2900xt/keiko-hackMIT/training/dataset/catalog/survey_registries_endpoints.md

# Machine-readable marine bioacoustics data sources — verified catalogue (checked 2026-09-19)

Legend: **V** = I fetched the page / listed the bucket / hit the API myself. **U** = unverified (from search snippets or secondary sources only). Sizes marked ">=" come from bucket scans that I capped at 12,000 objects.

## Headline findings
1. **Watkins (WHOI) is offline right now.** Both `cis.whoi.edu` and the `whoicf2.whoi.edu` mirror 302-redirect to `https://maintenance.whoi.edu` (curl + WebFetch, 2026-09-19). Everything below about its URL patterns comes from the Wayback Machine capture of 2024-08-10 (`web.archive.org/web/20240810115606id_/...`). The BEANS GCS zip (882 MB) and the Hugging Face parquet mirrors are the working fallbacks.
2. **The NCEI Google Cloud bucket `noaa-passive-bioacoustic` is the single richest anonymous endpoint**: it holds DCLDE 2011/2013/2015/2018/2022/2027, NEFSC, PIFSC, SanctSound, NRS, ADEON, JASCO, etc., all listable with no credentials via the JSON API.
3. **The Kaggle Watkins mirror (`shreyj1729/best-of-watkins-marine-mammal-sound-database`) returns 404** on both URL forms; treat it as gone. The Cornell/Right-Whale-Redux competition pages are JS-rendered (only `<meta>` text is fetchable), so their clip counts below are U.
4. **mobysound.org is dead** (parked Bluehost page). The DCLDE 2001–2013 archives it hosted are partially re-homed in the NCEI bucket (`dclde/2011/`, `dclde/2013/`).

## Master table

| Name | URL | Access | Format | Size | Species / scope | Labels | License | Download mechanics / URL patterns |
|---|---|---|---|---|---|---|---|---|
| **Watkins Marine Mammal Sound Database ("Best of" cuts)** V (via Wayback) | https://cis.whoi.edu/science/B/whalesounds/index.cfm (mirror: https://whoicf2.whoi.edu/science/B/whalesounds/) | Direct HTTP (currently down, maintenance redirect) | WAV, one file per cut; page table columns: `Sound cut file | Location | Observation Date | Download link | Metadata` | 1,694 cuts (about.cfm), 32 species; Internet-Archive zip of the 12 whale species is 646 MB | 32 species (list below) | Yes: species = page, plus per-cut location/date/metadata page | "free to download for personal or academic (not commercial) use. Reposting this work on third party websites is not permitted." Credit: "Watkins Marine Mammal Sound Database, Woods Hole Oceanographic Institution and the New Bedford Whaling Museum" | Species index page: `index.cfm` (dropdown `<option value="https://whoicf2.whoi.edu/science/B/whalesounds/bestOf.cfm?code=XXXX">`). Species page: `bestOf.cfm?code=AA3A` (54 WAV links on the N. right whale page). WAV href: `/science/B/whalesounds/WhaleSounds/<8-char id>.wav`, e.g. `https://cis.whoi.edu/science/B/whalesounds/WhaleSounds/5601601O.wav`, `.../56017007.wav`, `.../5900300A.wav` (id = 2-digit year + 3-digit tape + 3-char cut). Scraper that implements exactly this: https://github.com/AbdullahAbdelaziz122/watkins-mammal-scraper |
| **Watkins "All cuts"** V (Wayback) | `https://cis.whoi.edu/science/B/whalesounds/fullCuts.cfm` | Direct HTTP (down) | WAV | ~15,000 clips ("approximately 15,000 annotated digital sound clips"); HF mirror has 15,200 rows | 55 common names / 66 scientific-name codes (list below) | Yes | as above | Query pattern: `fullCuts.cfm?SP=<code>&YR=-1` (e.g. `fullCuts.cfm?SP=AC1E&YR=-1` = blue whale); master tapes at `masterFiles.cfm` |
| Watkins mirror: **BEANS zip** V | https://storage.googleapis.com/ml-bioacoustics-datasets/watkins.zip | Direct HTTP, no auth | WAV + `annotations.csv` (cols `path`, `species`) | 882,137,083 bytes | 32 species; BEANS drops Weddell_Seal (2 clips) -> 31 classes | Yes (CSV) | inherits Watkins terms | `wget https://storage.googleapis.com/ml-bioacoustics-datasets/watkins.zip && unzip watkins.zip -d watkins/` (this is exactly `scripts/watkins.py` in earthspecies/beans) |
| Watkins mirror: **HF DBD-research-group/beans_watkins** V | https://huggingface.co/datasets/DBD-research-group/beans_watkins | HF hub | parquet (train/train_low/valid/test) | 1K–10K rows | 31 classes (BEANS split) | Yes | not declared on card | `datasets.load_dataset("DBD-research-group/beans_watkins")` |
| Watkins mirror: **HF ivangtorre/watkins-marine-mammal-full-cuts** V | https://huggingface.co/datasets/ivangtorre/watkins-marine-mammal-full-cuts | HF hub | parquet, 9 shards, audio + nested metadata (record no., date, location+coords, signal/sound/animal dicts, sample rate 10–30 kHz) | 15,200 recordings | card says 54 species | Yes (species + Watkins metadata) | not declared | `load_dataset("ivangtorre/watkins-marine-mammal-full-cuts")` |
| Watkins mirror: **HF ardavey/marine_ocean_mammal_sound** V | https://huggingface.co/datasets/ardavey/marine_ocean_mammal_sound | HF hub | parquet | 1K–10K | 32 species (best-of) | Yes | card copies Watkins non-commercial text | `load_dataset("ardavey/marine_ocean_mammal_sound")` |
| Watkins mirror: **HF josegg5/watkins_marine_mammals_full** V | https://huggingface.co/datasets/josegg5/watkins_marine_mammals_full | HF hub | raw WAV in `Species/Year/<id>.wav` folders (127 files) | small (<1K) | partial | folder = species | tagged MIT (dubious relabel) | `huggingface-cli download josegg5/watkins_marine_mammals_full --repo-type dataset` |
| Watkins mirror: **Internet Archive watkins_best_of_whales_202008** V | https://archive.org/details/watkins_best_of_whales_202008 | Direct HTTP / torrent | per-species ZIPs | 646 MB total (`sperm_whale.zip` 446 MB, `short_finned_pilot_whale.zip` 121 MB, ... `minke_whale.zip` 48 KB) | 12 whale species only | folder = species | Watkins non-commercial | `https://archive.org/download/watkins_best_of_whales_202008/watkins_best_of_whales.zip`; metadata JSON at `https://archive.org/metadata/watkins_best_of_whales_202008` |
| Watkins **Kaggle mirror** (shreyj1729) | https://www.kaggle.com/datasets/shreyj1729/best-of-watkins-marine-mammal-sound-database | — | — | — | (55 folders per old descriptions) | — | — | **404 on 2026-09-19** (both `/datasets/` and `/shreyj1729/...` forms). Do not rely on it. |
| **DCLDE 2027 (ex-2026) killer whale dataset** V | GCS `gs://noaa-passive-bioacoustic/dclde/2027/dclde_2027_killer_whales/`; DOI https://doi.org/10.25921/15ey-mh50 (NCEI landing: `data.noaa.gov/metaview/page?xml=NOAA/NESDIS/NGDC/MGG/passive_acoustic//iso/xml/DCLDE_2027_Killer_Whales.xml&view=getDataView`); paper https://pmc.ncbi.nlm.nih.gov/articles/PMC12229703/ ; code https://zenodo.org/records/15743034 (10.5281/zenodo.15743034, MIT, 4.9 MB) | GCS anonymous | FLAC/WAV audio (16–256 kHz, provider-dependent) + `Annotations.csv` (50.5 MB) + per-provider `annotations/*.csv`, `metadata/*.pdf|txt` | paper: 1.6 TB, 225,000+ bounding-box annotations, 23 sites, May 2013–Apr 2023; my scan: >=253 GB in first 12,000 objects | *Orcinus orca* ecotypes SRKW, NRKW, TKW (Bigg's), OKW, SAR + humpback + abiotic + undetermined bio | Yes, CSV cols: `SoundFile, FilePath, FileBeginSec, FileEndSec, LowFreqHz, HighFreqHz, UTC, ClassSpecies, AnnotationLevel, KW, KW_certain, Ecotype, Data Provider, Dataset`; ClassSpecies in {KW, HW, AB, UndBio} | Bucket contains `CC-BY-4.0.txt`; the Sci Data paper states CC BY-NC-ND 4.0 — conflicting, check before commercial use | `gsutil -m cp -r gs://noaa-passive-bioacoustic/dclde/2027/dclde_2027_killer_whales/Annotations.csv .`; list: `curl "https://storage.googleapis.com/storage/v1/b/noaa-passive-bioacoustic/o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"`. Provider subfolders seen: `dfo_crp/`, `dfo_wdlp/` (files like `SOGN-AMAR-610_annotations.csv`) |
| **DCLDE 2027 NARW Cape Cod Bay** V | `gs://noaa-passive-bioacoustic/dclde/2027/dclde2027_narw_detections_in_cape_cod_bay/` + `.../dclde2027_acoustic_monitoring_in_cape_cod_bay/audio/` | GCS anonymous | Raven selection tables `data/YYYYMMDD.selections.txt` (122 objects, 0.3 GB) + 2 kHz FLAC 15-min files `85941ORSUCCB01_002K_M05_multi_20190215_155344Z.flac` (~3.3 MB each) | annotations 0.3 GB; audio Feb–Mar 2019 | North Atlantic right whale upcalls | Yes (Raven) | NOAA (public) | `gsutil -m cp -r gs://noaa-passive-bioacoustic/dclde/2027/dclde2027_narw_detections_in_cape_cod_bay/ .` |
| **DCLDE 2027 DAS fin-whale localization** V | `gs://noaa-passive-bioacoustic/dclde/2027/dclde_2027_das-finwhale-localization/` | GCS anonymous | DAS data + `annotations/batch1|batch2/annotated_calls_{north,south}_<timestamp>.csv` | 242 objects, 103.1 GB | fin whale 20 Hz calls (OOI DAS cable, Nov 2021) | Yes (CSV) | NOAA | as above |
| **DCLDE 2024 (Rotterdam)** V page | http://www.dclde2024.com/data-sets/ | **Request**: credentials in the dataset report (v5.0-1) downloaded from the page; weekly transfer via dclde2024@gmail.com; hosted on DRDC site | sonobuoy audio + CSV submission format | not stated ("batch download in progress") | NARW, Gulf of St Lawrence 2018, 2 x 3.5 h fields of 32 sonobuoys + visual/glider data | Yes | none stated | Not in the NCEI bucket (no `dclde/2024/` prefix). |
| **DCLDE 2022 (Oahu, HICEAS 2017)** V bucket | `gs://noaa-passive-bioacoustic/dclde/2022/dclde_2022_1705/` and `.../dclde_2022_1706/`; NCEI `gov.noaa.ncei.pad:DCLDE_2022_Raw_Data`; https://www.soest.hawaii.edu/ore/dclde/dataset/ (ECONNREFUSED on test) | GCS anonymous | WAV/FLAC towed-array multichannel | >=2.2 TB scanned (truncated); SOEST says ~8 TB uncompressed / 4 TB FLAC | beaked whales, minke boings, delphinids etc., Hawaiian EEZ Jul–Nov 2017 | Yes per SOEST (encounter tables); annotation files not located in my scan | NOAA | `gsutil ls gs://noaa-passive-bioacoustic/dclde/2022/` |
| **DCLDE 2018 (Paris)** V | https://sabiod.lis-lab.fr/DCLDE/challenge.html (self-signed cert; use `curl -k`) + `gs://noaa-passive-bioacoustic/dclde/2018/{audio,products}/` | Direct HTTP + Google Drive + GCS; HF audio originally by mailed 4 TB disk | WAV `WAT_HZ_01_151014_055500.x.wav` (200 kHz HF) / `HAT_A_02_121021_000000.d100.x.wav` (2 kHz LF); CSV annotations | GCS products 106 objects; audio prefix present (not sized) | HF: Gervais', Cuvier's, Sowerby's beaked whales, Atlantic white-sided, Risso's, short-finned pilot, *Stenella* sp., Delphinid A/B, unid. delphinid. LF: blue whale tonal, NARW upcall | Yes | none stated | LF annotations direct: `https://sabiod.lis-lab.fr/DCLDE/data/DCL_LF_Data_traindev/annotations/LF_Annotations_Dev.zip`; LF WAV Google Drive ids `1OPt9UXgWL6KpZpRekNdg_CeK4MONW5o3`, `1aHWlxViFktIoKqz-ObQB3NNuqp_wt5fb`, `1w9GumQTwkCDNKd_Vj24wT-Cx0i42tsBj`; scoring tools `files/dclde2018-scoringtools.zip`; NCEI CSVs e.g. `dclde/2018/products/detections/dclde_2018_hat-a_annotations_hf_dev/data/HAT_A_HF_dev.csv` (sites GofMX-DT, HAT-A, ...) |
| **DCLDE 2015 (San Diego)** V | https://www.cetus.ucsd.edu/dclde/dataset.html + `gs://noaa-passive-bioacoustic/dclde/2015/{audio,products}/` | Google Drive (LF) / mailed 4 TB disk via dcldeworkshop@gmail.com (HF) / GCS | HARP WAV; CSV call-level annotations | LF ~29 GB; GCS products 211 objects 4.5 GB | LF: blue whale D calls, fin 40 Hz; HF: Cuvier's & Baird's beaked, Risso's, Pacific white-sided, sperm, porpoise (to 160 kHz) | Yes | none stated | Drive: data `0B9myW-wOt9CLcVBvN01jNWFSQ0U`, annotations `0B9myW-wOt9CLQ2lyXzdkeVRoYWc`; GCS CSVs e.g. `dclde/2015/products/detections/dclde_2015_cinms-b_annotations_lf_eval/data/CINMS-B.csv` (sites CINMS-B, CINMS-C, DCPP-A, ...) |
| **DCLDE 2013 (St Andrews)** V | https://research-portal.st-andrews.ac.uk/en/datasets/dclde-2013-workshop-dataset/ (DOI 10.17630/62c3eebc-5574-4ec0-bfef-367ad839fe1a) and `gs://noaa-passive-bioacoustic/dclde/2013/nefsc_sbnms_200903_nopp6_ch10/` (NCEI DOI 10.25921/zaea-1s39) | Direct HTTP / GCS | WAV 15-min mono 2 kHz 16-bit (`NOPP6_EST_20090328_000000_CH10.wav`, 3,600,044 B each) + CSV logs | ~3.3 GB (St Andrews) | NARW upcalls, Cape Cod Bay / Great South Channel 2000–2009; SBNMS Mar 2009 all-baleen log | Yes: `detections/..._upcall-detection-log.csv`, `..._allbaleen_detection_log_updated-2025-07-02.csv` | CC BY (St Andrews) | `gsutil -m cp -r gs://noaa-passive-bioacoustic/dclde/2013/ .` |
| DCLDE 2011 | `gs://noaa-passive-bioacoustic/dclde/2011/` | GCS | — | not explored | Mt Hood workshop data | — | NOAA | prefix exists (listed) |
| **MobySound / DCL 2003–2009** | https://www.mobysound.org/workshops.html | **dead** | — | — | — | — | — | Domain is a parked Bluehost page (curl 2026-09-19). |
| **Orcasound live/archival audio** V | https://github.com/orcasound/orcadata (access.md) | S3 anonymous (`--no-sign-request`) | HLS `.ts` segments + `live.m3u8`; FLAC lossless (48/96/192 kHz) in archive bucket | continuous since 2018 (not sized) | SRKW habitat, 8 nodes | No (raw) | code AGPL-3.0; data CC BY-NC-SA per UKAN listing (U) | Buckets: `audio-orcasound-net` (live: `rpi_{andrews_bay,bush_point,mast_center,north_sjc,orcasound_lab,point_robinson,port_townsend,sunset_bay}/hls/<unix_ts>/`), `audio-deriv-orcasound-net`, legacy `streaming-orcasound-net`, `dev-streaming-orcasound-net`, `archive-orcasound-net` (FLAC; only `rpi_port_townsend/` present), `acoustic-sandbox`, `visual-sandbox`, `orcagsoc`. `aws --no-sign-request s3 ls s3://audio-orcasound-net/rpi_orcasound_lab/hls/` ; browse at https://open.quiltdata.com/b/acoustic-sandbox |
| **Orcasound Pod.Cast labeled rounds** V | https://github.com/orcasound/orcadata/wiki/Pod.Cast-data-archive ; `s3://acoustic-sandbox/labeled-data/detection/` | S3 anonymous | 20 kHz WAV + TSV (`dataset, wav_filename, start_time_s, duration_s, location, date, pst_or_master_tape_identifier`; positives only) | `train/TrainDataLatest_PodCastAllRounds_123567910.tar.gz` 5,461,870,195 B (8 rounds); `TrainDataLatest_PodCastAllRounds_123567.tar.gz` 3.5 GB; `TrainDataLatest_PodCastAllRounds.tar.gz` 2.13 GB; `TestDataLatest_PodCastAllRounds_123.tar.gz` 1.08 GB; `WHOIS09222019_PodCastRound1.tar.gz` 1.73 GB; `OrcasoundLab07052019_PodCastRound2.tar.gz` 259 MB; `OrcasoundLab09272017_PodCastRound3.tar.gz` 418 MB; `test/OS_SVeirs_07_05_2019_08_24_00.tar.gz` 134 MB; `test/OrcasoundLab09272017_Test.tar.gz` 95 MB; TSVs `podcast2.tsv`, `podcast3.tsv`, `test.tsv` | SRKW calls (binary) | Yes (TSV) | Round 1 is Watkins KW data with "different license"; rest Orcasound | `aws --no-sign-request s3 cp s3://acoustic-sandbox/labeled-data/detection/train/TrainDataLatest_PodCastAllRounds_123567910.tar.gz .` or `git clone https://github.com/orcasound/orcaml && python orcaml/data_ml/tools/download_datasets.py <dir>` |
| Orcasound classification sandbox V | `s3://acoustic-sandbox/labeled-data/classification/killer-whales/{biggs-transients,global-general/WMMSD,northern-residents,offshores,southern-residents}/` | S3 anonymous | e.g. `southern-residents/20190705/orcasound-lab/OS_7_05_2019_08_54_00_.wav` (317 MB) + Audacity label txt (`..._labels-SV_200210_only_calls.txt`) | few GB | KW ecotypes | partial | Orcasound | as above |
| Orcasound SRKW call catalog V | https://www.orcasound.net/data/product/SRKW/call-catalog/srkw-orca-call-catalog.html ; repo `orcadata/Sounds/catalog` | Direct HTTP / git | FLAC/OGG/MP3 + spectrograms | small | 41 SRKW call types S01–S46 (Ford 1987/Osborne) | call-type = file | not stated | git clone orcadata |
| **Kaggle Cornell Whale Detection Challenge (2013)** V page (JS-rendered) | https://www.kaggle.com/c/whale-detection-challenge/data | Kaggle account + accept rules | AIFF 2-s clips at 2 kHz; `train.csv` labels (U: 30,000 train / 54,503 test clips) | ~1 GB (U) | NARW upcall vs noise | Yes (binary CSV) | competition rules | `kaggle competitions download -c whale-detection-challenge`. Alt mirror: https://www.timeseriesclassification.com/description.php?Dataset=RightWhaleCalls |
| **Kaggle ICML 2013 Right Whale Redux** V page (JS) | https://www.kaggle.com/c/the-icml-2013-whale-challenge-right-whale-redux | Kaggle account | AIFF (U) | (U) | NARW upcall | Yes | competition rules | `kaggle competitions download -c the-icml-2013-whale-challenge-right-whale-redux` |
| **NOAA NCEI Passive Acoustic Data archive (GCS)** V | https://www.ncei.noaa.gov/products/passive-acoustic-data ; map https://www.ncei.noaa.gov/maps/passive-acoustic-data/ ; bucket https://console.cloud.google.com/storage/browser/noaa-passive-bioacoustic | GCS anonymous (also request via pad.info@noaa.gov) | WAV/FLAC/XWAV-in-FLAC; products netCDF + CSV | >100 TB total (NCEI) | 29 top-level prefixes: `MD_WEA_CPOD, adeon, aeon, afsc, big_query_metadata, boem, coastal_studies_institute, cornell, dclde, esons, fram, jasco, listen, mbarc_arctic, mbarc_cencal, mbarc_flip, mbarc_socal, mbari, navy, nefsc, nps, nrs, onms, pifsc, rutgers_njrmi, sanctsound, sefsc, soundcoop, swfsc` | per project; inventory CSVs in `big_query_metadata/` (`NCEI_NEFSC_PAD_metadata.csv` 33 MB, `NCEI_AFSC_PAD_metadata.csv`, `NCEI_SANCTSOUND_PAD_metadata.csv`, `NCEI_NRS_PAD_metadata.xlsx`, `NCEI_ADEON_PAD_metadata.xlsx`) | NOAA public domain / CC0 (SanctSound) | List: `curl "https://storage.googleapis.com/storage/v1/b/noaa-passive-bioacoustic/o?delimiter=/&prefix=<p>"`; fetch: `https://storage.googleapis.com/noaa-passive-bioacoustic/<object>`; `gsutil -m cp -r gs://noaa-passive-bioacoustic/<prefix> .` ; root `README.pdf` |
| **NEFSC annotated baleen datasets** V | https://www.fisheries.noaa.gov/resource/data/noaa-nefsc-north-atlantic-right-whale-acoustic-data-and-annotations ; `gs://noaa-passive-bioacoustic/nefsc/{audio,products}/` | GCS anonymous | multichannel audio + Raven-derived CSV logs (`Detected` / `Possibly_Detected`) | `nefsc/products/` = 4,316 objects, 32.4 GB (detections + sound_level_metrics netCDF) | NARW upcalls, humpback song, sei downsweeps, fin 20 Hz, minke pulse trains, blue A/B/AB | Yes: `nefsc/products/detections/nefsc_baleen/<deployment>_narw/data/<DEPLOY>_upcall-detection-log.csv` (e.g. `NEFSC_GA_201510_CH1_20160108_upcall-detection-log.csv`, `NEFSC_SBNMS_200712_NOPP1_CH10_20080127_...`, `NEFSC_NC_201712_HATTERAS_CH2_20180121_...`) | NOAA public | `gsutil -m cp -r gs://noaa-passive-bioacoustic/nefsc/products/detections/ .` ; deployment inventory (U, from search): `https://storage.googleapis.com/nmfs_odp_nefsc/PARR/READ/PSB/24687/24687_NEFSC_Acoustic_Deployments.xlsx`; PACM viewer https://apps-nefsc.fisheries.noaa.gov/pacm/ |
| **NOAA PIFSC HARP humpback set (Google model training data)** V | `gs://noaa-passive-bioacoustic/pifsc/` (README.md); DOI 10.25921/Z787-9Y54 | GCS anonymous | FLAC-compressed XWAV (75-s subchunks, 10 kHz; decompress with `flac -d --keep-foreign-metadata`) + `annotations.csv` | 9.2 TB (Google blog) | humpback song + confusers, 12 Pacific Islands sites, ~15 y | Yes: cols `audit_name, flac_compressed_xwav_object, subchunk_index, label_is_strong, ...` (Allen et al. 2021 Table 1) | NOAA public | `gsutil cp gs://noaa-passive-bioacoustic/pifsc/README.md .` |
| **SanctSound (NOAA/Navy)** V | https://catalog.data.gov/dataset/sanctsound-raw-passive-acoustic-data ; DOI 10.25921/saca-sp25 ; https://sanctsound.ioos.us/ | GCS anonymous | audio + per-detection CSV + netCDF | not stated; 30 sites x deployments 2018–21 | 7 sanctuaries + 1 monument; detection products per species (bluewhale, bocaccio, humpback, ...) | Yes | CC0 | `gs://noaa-passive-bioacoustic/sanctsound/audio/<site>/sanctsound_<site>_<dep>/` ; `.../products/detections/<site>/sanctsound_<site>_<dep>_<species>/data/SanctSound_<SITE>_<dep>_<species>.csv|.nc` (sites ci01–05, fk01–04, gr01–03, hi01,03–06, mb01–03, oc01–04, pm01,02,05,08, sb01–03) |
| **Google humpback whale model** V slug | https://www.kaggle.com/models/google/humpback-whale ; https://arxiv.org/abs/2512.03219 (Perch/whale) | Kaggle (kagglehub, free account) | TF2 SavedModel; 10 kHz input | — | humpback (trained on PIFSC HARP above) | model | Kaggle page JS-rendered; Apache-2.0 per perch repo (U) | `kagglehub.model_download("google/humpback-whale/tensorFlow2/humpback-whale")` (slug verified in perch-hoplite `kaggle_hub.py`) |
| **Google multispecies whale model** V | https://www.kaggle.com/models/google/multispecies-whale ; https://research.google/blog/whistles-songs-boings-and-biotwangs-recognizing-whale-vocalizations-with-ai/ | Kaggle | TF2 SavedModel | — | 8 species / 12 classes: humpback, killer whale (+echolocation, whistles), blue, fin, minke (boing), Bryde's (biotwang), N. Atlantic right, N. Pacific right (gunshot, upcall); training data from PIFSC, MBARI MARS, DFO Salish Sea, AFSC, NEFSC | model | as above | `kagglehub.model_download("google/multispecies-whale/tensorFlow2/default")`; hoplite key `multispecies_whale` |
| **Perch 2.0** V | https://www.kaggle.com/models/google/bird-vocalization-classifier (variant perch_v2) ; https://github.com/google-research/perch-hoplite ; paper https://arxiv.org/abs/2512.03219 | Kaggle | TF2 (GPU/CPU variants), ONNX port on HF | ~12M params EfficientNet-B3 | 14,597 species incl. mammals; whale transfer evaluated on Watkins/BEANS | model | Apache-2.0 (U) | `pip install git+https://github.com/google-research/perch-hoplite.git`; `model_configs.load_model_by_name('perch_v2')` -> slug `google/bird-vocalization-classifier/tensorFlow2/perch_v2` (or `perch_v2_cpu`); SurfPerch: `google/surfperch/TensorFlow2/1` |
| **MBARI MARS "pacific-sound" (AWS Open Data)** V | https://registry.opendata.aws/pacific-sound/ ; https://docs.mbari.org/pacific-sound/ | S3 anonymous, region us-west-2 | WAV: 16 kHz daily `s3://pacific-sound-16khz/YYYY/MM/MARS-YYYYMMDDT000000Z-16kHz.wav` (4,147,200,332 B/day); 2 kHz daily `s3://pacific-sound-2khz/YYYY/MM/MARS-YYYYMMDDT000000Z-2kHz.wav` (518 MB/day); raw 256 kHz 10-min `s3://pacific-sound-256khz-YYYY/MM/MARS_YYYYMMDD_HHMMSS.wav` (461 MB) | 2015–2026 continuous (~1.5 TB/yr at 16 kHz) | Monterey Bay: blue, fin, humpback, orca, dolphins, ships | Labeled subsets via docs notebooks (blue-whale call index, fin index, humpback song); models in `s3://pacific-sound-models/` (`bluewhale-a-resnet50-2022-02-05-...tar.gz` 254 MB, `bluewhale-d-efnetb0-...` 46 MB, etc.) | CC-BY 4.0 | `aws s3 ls --no-sign-request s3://pacific-sound-16khz/2023/01/` ; `aws s3 cp --no-sign-request s3://pacific-sound-2khz/2023/01/MARS-20230101T000000Z-2kHz.wav .` |
| **Ocean Networks Canada Oceans 3.0 API** V | https://oceannetworkscanada.github.io/Oceans3.0-API/API_Guide.html ; OpenAPI https://data.oceannetworks.ca/OpenAPI ; UI https://data.oceannetworks.ca/SearchHydrophoneData | **Registration** (free token: data.oceannetworks.ca/Registration -> Profile -> Web Services API -> Copy Token) | WAV/FLAC/MP3 archive files + spectrogram PNG; data products generated on demand | multi-year cabled hydrophones (BC coast, Arctic) | Salish Sea/Barkley Canyon etc. | No (raw); ONC-derived labels exist in HF `bnestor/marine_mammal_labels` (8,761 JSON, CC-BY-4.0, filenames like `ICLISTENAF2523_20160523T094302.000Z_...json`) | CC-BY-ND per UKAN (U); client Apache-2.0 | `pip install onc`; `from onc import ONC; onc=ONC(token); onc.getLocations({"deviceCategoryCode":"HYDROPHONE"}); onc.getArchivefileByLocation({...}); onc.downloadArchivefile(filename)`; endpoints `/api/archivefile`, `/api/dataProductDelivery` (request->run->download, or `orderDataProduct()`); last-hour WAVs withheld |
| **OOI hydrophones (Regional Cabled / Endurance)** V root | https://rawdata.oceanobservatories.org/files/ ; https://github.com/Ocean-Data-Lab/ooipy ; https://ooipy.readthedocs.io/ | Direct HTTP (raw data server; not in M2M API) | miniSEED 5-min files (broadband 64 kHz; low-freq 200 Hz) | 1.8 GB/hour broadband | NE Pacific (Oregon slope/axial): fin, blue, humpback, sperm, ships | No | OOI open data (CC0/public, U) | Directory tree `https://rawdata.oceanobservatories.org/files/<SITE>/<NODE>/<INSTR>/YYYY/MM/DD/` e.g. `RS01SLBS/LJ01A/09-HYDBBA102/` (site codes listed at root: AS03CPPM, CE01ISSM, CE02SHBP, CE04OSBP, RS01..., ...). `pip install ooipy; ooipy.get_acoustic_data(start,end,'LJ01A')` |
| **BEANS benchmark (earthspecies)** V | https://github.com/earthspecies/beans ; datasets.yml | mixed: GCS zips (marine ones) + Kaggle CLI (cbi, rcfx) | WAV + CSV splits | whole benchmark ~300 GB; marine parts: `watkins.zip` 882 MB, `hiceas_1-20_minke-detection.zip` 1,424,628,433 B | marine subsets: **watkins** (classification, 31 species, 44.1 kHz, <=3 s) and **hiceas** (detection, 1 label: minke boings, HICEAS towed array) | Yes | code MIT; data per source | `bash scripts/download_data.sh` (needs `~/.kaggle/kaggle.json`, sox); direct: `wget https://storage.googleapis.com/ml-bioacoustics-datasets/hiceas_1-20_minke-detection.zip` |
| **ANIMAL-SPOT data** V | https://github.com/ChristianBergler/ANIMAL-SPOT ; data DOI https://doi.org/10.17617/3.KQPPXF (Edmond/MPG Dataverse) | Direct HTTP (Dataverse) | `ANIMAL-SPOT_FILES.tar.gz` 547.4 MB (cropped audio, unseen prediction tape, splits, logs) | 547 MB | multi-species incl. orca (~5,000 samples/species) | Yes | CC BY 4.0 | Dataverse API: `https://edmond.mpg.de/api/datasets/:persistentId/?persistentId=doi:10.17617/3.KQPPXF` -> file id -> `/api/access/datafile/<id>` |
| **ORCA-SPOT** V | https://github.com/ChristianBergler/ORCA-SPOT | code only | — | trained on 11,509 KW signals + 34,848 noise (Orchive/OrcaLab NRKW) | NRKW | training data **not public** | GPL-3.0 (code) | Orchive (http://orchive.cs.uvic.ca/) availability uncertain |
| **Antarctic blue/fin whale annotated library (AAD)** V | https://data.aad.gov.au/metadata/records/fulldisplay/AcousticTrends_BlueFinLibrary ; DOI 10.26179/5e6056035c01b | Direct HTTP | 16-bit WAV at 250/500/1000/2000 Hz + Raven Pro 1.5 selection tables (TSV) | 1,880 h, 11 site-years 2005–2017, 105,161 annotations | Antarctic blue & fin whale calls (7 call types) | Yes | CC BY 4.0 | `https://data.aad.gov.au/eds/5091/download` |
| HF **monster-monash/WhaleSounds** V | https://huggingface.co/datasets/monster-monash/WhaleSounds | HF hub | `.npy`/CSV, 105,163 x 2,500 samples @250 Hz | 3.57 GB | 8 classes (7 Antarctic call types + unidentified), derived from AAD library | Yes | CC BY 4.0 | `load_dataset("monster-monash/WhaleSounds")` |
| HF **CIANLabxBROWNUniv/fin_whale_1** V | https://huggingface.co/datasets/CIANLabxBROWNUniv/fin_whale_1 | HF hub | 7,118 files (code + data) | — | fin whale detection (SSL vs supervised paper) | Yes | MIT | `huggingface-cli download ...` |
| **FRDR NARW upcalls Gulf of St Lawrence** V | https://www.frdr-dfdr.ca/repo/dataset/4a3113e6-1d58-6bb4-aaf2-a9adf75165be (DOI 10.20383/101.0241) | Globus (account) or zip (was unavailable) | audio + spectrograms + presence/absence annotations | not stated | NARW, 6 stations 2015–2019 + Gulf of Maine 2009 | Yes | CC BY 4.0 | Globus transfer |
| **DOCC10 (Dyni odontocete click classification)** V | https://challengedata.ens.fr/challenges/32 | **Registration** | raw click frames 8,192 samples @200 kHz | train ~6 GB; 11,312/class train, 2,096/class test | 10 classes: Risso's, short-finned pilot, Atl. white-sided, Sowerby's, Gervais', sperm whale, *Stenella*, delphinid A/B, Cuvier's (9 from DCLDE 2018 + DYNI Med sperm whales) | Yes (balanced) | not stated | login required |
| **Zenodo hits** (titles from search; only 15743034 fetched) | 10.5281/zenodo.20702261 glider PAM Cabrera (51.2 h @240 kHz, sperm/Risso's clicks + whistles, annotated) U; 10.5281/zenodo.22649833 E. Med dolphin whistle clips (713 common + 222 bottlenose) U; 10.5281/zenodo.10665971 Placentia Bay acoustic features U; 10.5281/zenodo.7886409 DAS + hydrophone array U; 10.5281/zenodo.5841998 porpoise hydrophone clusters (windfarm) U; 10.5281/zenodo.5823343 DAS4Whales U; 10.5281/zenodo.15743034 DCLDE code V (MIT) | Direct HTTP | mixed | — | — | — | — | Zenodo REST: `https://zenodo.org/api/records?q=<terms>&size=25` (note: complex boolean queries returned 400 / off-topic ranking; search manually) |
| **Dryad hits** V (API) | doi:10.5061/dryad.v9s4mw6xv harbour porpoise hydrophone array on gill net (6.76 GB, CC0); doi:10.5061/dryad.98sf7m0mn coastal acoustic buoy cetacean detections (9.85 GB, CC0); doi:10.5061/dryad.7h44j0zvq porpoise directional clusters at windfarms (U); doi:10.5061/dryad.3bk3j9kn8 Placentia Bay PAM features (U) | Direct HTTP | WAV/CSV | as listed | porpoise / cetacean | partial | CC0 | `https://datadryad.org/api/v2/search?q=cetacean+acoustic+recordings+hydrophone` |
| **Figshare** | Sci Data bottlenose dolphin trawling WAV dataset (s41597-023-02547-8, 192 kHz) U | Direct HTTP | WAV | — | *Tursiops* whistles/clicks/pulses | Yes | CC BY (U) | Figshare API search (`POST /v2/articles/search`) returned no relevant hits for my query; locate via the paper's Data Availability |
| **PANGAEA** V (API) | https://doi.pangaea.de/10.1594/PANGAEA.773610 PALAOA soundscape 2005–2011 (links to audio stream files, CC BY 3.0); 10.1594/PANGAEA.861766 PASATA field documentation (CC BY 3.0) | Direct HTTP | audio streams / docs | — | Antarctic (Weddell seals, leopard seals, orcas, minke) | No/partial | CC BY 3.0 | `https://www.pangaea.de/advanced/search.php?q=hydrophone+marine+mammal&count=15` (JSON) |
| **GBIF sound occurrences (marine)** V | https://api.gbif.org/v1/occurrence/search?taxonKey=733&mediaType=Sound | API, no auth | JSON with `media[].identifier` -> iNat `.m4a` | Cetacea (taxonKey 733): **120** sound occurrences (71 from iNaturalist dataset `50c9509d-22c7-4a22-a47d-8c48425ef4a7`, 30 from `f11db245-...`, 11 from `b7ec1bf8-...`); Pinnipedia (4941589): 0 | orca, harbour porpoise, humpback, etc. | species = label | per record (CC BY-NC mostly) | `&facet=datasetKey`, `&limit=300&offset=N` |
| **iNaturalist sounds** V | https://api.inaturalist.org/v1/observations?taxon_id=152871&sounds=true&quality_grade=research | API, no auth | `.m4a`/`.wav` at `https://static.inaturalist.org/sounds/<id>.m4a` | 128 obs (85 research-grade) for Cetacea | e.g. *Aethalodelphis obliquidens*, humpback | species | per obs (cc0, cc-by-nc, ...) | paginate `per_page=200&page=N`; `sounds[].file_url` |
| **Macaulay Library** | https://search.macaulaylibrary.org/catalog?mediaType=audio&taxonCode=<code> | Registration + cart request for originals; CSV metadata export | WAV/MP3 originals by request | ~2,159 Cetacea audio + 312 video (U) | cetaceans, sirenians, pinnipeds | species + metadata | ML terms (research request) | No bulk API; site 403s to bots |
| **DOSITS audio gallery** | https://dosits.org/galleries/audio-gallery/marine-mammals/ (403 to bots) | Direct HTTP (browser) | MP3 per species page | small | baleen, toothed, pinnipeds, sirenians | species page | per-file copyright (not bulk-licensed) | not machine-friendly |
| **Freesound MBARI_MARS pack** V | https://freesound.org/people/MBARI_MARS/packs/19487/ | Registration (login to download) / API token | WAV/FLAC | 12+ sounds | humpback, blue, gray, sperm, beaked, orca, Pacific white-sided | tags | per-sound CC | Freesound API `https://freesound.org/apiv2/search/text/?query=hydrophone&token=...`; other packs: klankbeeld 26803, 14861 |
| **IMOS acoustic observatories (AODN)** V | https://acoustic.aodn.org.au/acoustic/ ; S3 `s3://imos-data/IMOS/ANMN/Acoustic/` (ap-southeast-2) | S3 anonymous / portal | raw Curtin noise-logger `.DAT` (~2.4 MB each) + spectrogram PNG; Matlab reader in `code/`; `calibration/`, `metadata/` | 2008–2017 (ceased) | sites PAKAI (Kangaroo I.), PAKIM (Kimberley), PAPCA (Perth Canyon), PAPIL (Pilbara), PAPOR (Portland), PATUN (Tuncurry); pygmy blue, fin, humpback | No | IMOS CC-BY (U) | `aws s3 ls --no-sign-request s3://imos-data/IMOS/ANMN/Acoustic/PAPCA/2802/20080226/raw/` ; http listing `https://s3-ap-southeast-2.amazonaws.com/imos-data/?prefix=IMOS/ANMN/Acoustic/` |
| **JASCO** | https://www.jasco.com/public-reports | none open | — | — | contributed JASCO/VFPA orca data to DCLDE 2027; `jasco/audio/` prefix exists in NCEI bucket (V) | — | — | no public dataset endpoint |
| **AcousticNet** | — | — | — | — | **no such resource found** in 2 searches | — | — | — |
| **Marine Mammal Commission** | https://www.mmc.gov/wp-content/uploads/sound_bklet.pdf | — | PDF only | — | no data | — | — | not a data source |
| **UK Acoustics Network open-data list** V | https://acoustics.ac.uk/open-access-underwater-acoustics-data/ | index page | — | 95 entries (DCL/DCLDE, ALOHA, LoVe, Galway Bay, SOHN, OHA-SIS-BIO, DAS4Whales, ShipsEar, DeepShip...) | — | — | — | best secondary aggregator found |

## Species-name lists (verbatim from fetched pages)

### Watkins "Best of" cuts — code -> common name (index.cfm dropdown, Wayback 2024-08-10)
```
AA1A  Bowhead Whale                       BD15L Spinner Dolphin
AA3A  Northern Right Whale                BD17A Rough-Toothed Dolphin
AA3B  Southern Right Whale                BD19D Bottlenose Dolphin
AC1A  Minke Whale                         BD3B  Common Dolphin
AC1F  Fin, Finback Whale                  BD4A  Grampus, Risso's Dolphin
AC2A  Humpback Whale                      BD5A  Fraser's Dolphin
BA2A  Sperm Whale                         BD6A  White-sided Dolphin
BB1A  Beluga, White Whale                 BD6B  White-beaked Dolphin
BB2A  Narwhal                             BE3C  Long-Finned Pilot Whale
BD10A Melon Headed Whale                  BE3D  Short-Finned (Pacific) Pilot Whale
BD15A Pantropical Spotted Dolphin         BE7A  Killer Whale
BD15B Clymene Dolphin                     BE9A  False Killer Whale
BD15C Striped Dolphin                     CB1A  Walrus
BD15F Atlantic Spotted Dolphin            CC12G Harp Seal
                                          CC14A Ross Seal
                                          CC2A  Bearded Seal
                                          CC4A  Leopard Seal
                                          CC5A  Weddell Seal
```
Scientific names on the same page: AA1A *Balaena mysticetus*; AC1A *Balaenoptera acutorostrata*; AC1F *Balaenoptera physalus*; BB1A *Delphinapterus leucas*; BD3B *Delphinus delphis*; CC2A *Erignathus barbatus*; AA3B *Eubalaena australis*; AA3A *Eubalaena glacialis*; BE3C *Globicephala melas (Globicephala melaena, Globicephala edwardii)*; BE3D *Globicephala macrorhynchus (Globicephala scammoni)*; BD4A *Grampus griseus*; CC4A *Hydrurga leptonyx*; BD5A *Lagenodelphis hosei*; BD6A *Lagenorhynchus acutus*; BD6B *Lagenorhynchus albirostris*; CC5A *Leptonychotes weddellii*; AC2A *Megaptera novaeangliae*; BB2A *Monodon monoceros*; CB1A *Odobenus rosmarus*; CC14A *Ommatophoca rossi*; BE7A *Orcinus orca*; BD10A *Peponocephala electra*; CC12G *Pagophilus groenlandicus (Phoca groenlandica)*; BA2A *Physeter macrocephalus (Physeter catodon)*; BE9A *Pseudorca crassidens*; BD15A *Stenella attenuata*; BD15B *Stenella clymene*; BD15C *Stenella coeruleoalba*; BD15F *Stenella frontalis*; BD15L *Stenella longirostris*; BD17A *Steno bredanensis*; BD19D *Tursiops truncatus (Tursiops gilli)*.

### Watkins "All cuts" — code -> common name (fullCuts.cfm dropdown; query `fullCuts.cfm?SP=<code>&YR=-1`)
```
BD15F Atlantic Spotted Dolphin      CC2A  Bearded Seal              BB1A  Beluga, White Whale
AC1E  Blue Whale                    BD19D Bottlenose Dolphin        BG2A  Boutu, Amazon River Dolphin
AA1A  Bowhead Whale                 BD15B Clymene Dolphin           BD1A  Commerson's Dolphin
BD3B  Common Dolphin                BF4A  Dall's Porpoise           BD6H  Dusky Dolphin
BE9A  False Killer Whale            AC1F  Fin, Finback Whale        BF6A  Finless Porpoise
BD5A  Fraser's Dolphin              BD4A  Grampus, Risso's Dolphin  CC3A  Gray Seal
AB1A  Gray Whale                    BF2A  Harbor Porpoise           CC12V Harbour Seal
CC12G Harp Seal                     BD1C  Heaviside's Dolphin       CC1A  Hooded Seal
AC2A  Humpback Whale                BD12A Irawaddy Dolphin          CA1P  Juan Fernandez Fur Seal
BE7A  Killer Whale                  CC4A  Leopard Seal              BD3A  Long Beaked (Pacific) Common Dolphin
BE3C  Long-Finned Pilot Whale       BD10A Melon Headed Whale        AC1A  Minke Whale
BB2A  Narwhal                       CA1F  New Zealand Fur Seal      AA3A  Northern Right Whale
BD15A Pantropical Spotted Dolphin   CC12F Ribbon Seal               CC12H Ringed Seal
CC14A Ross Seal                     BD17A Rough-Toothed Dolphin     CD1A  Sea Otter
BE3D  Short-Finned (Pacific) Pilot Whale   AA3B Southern Right Whale   BA2A Sperm Whale
BD15L Spinner Dolphin               CC12L Spotted Seal              CA3B  Steller Sea Lion
BD15C Striped Dolphin               BD12B Tucuxi Dolphin            CB1A  Walrus
CC5A  Weddell Seal                  DB1B  West Indian Manatee       BD6B  White-beaked Dolphin
BD6A  White-sided Dolphin
```
Additional scientific-name codes present only in the All-cuts scientific dropdown (no common-name entry): CA2A *Callorhinus ursinus*; BE3A *Globicephala malaena (Globicephala edwardii)*; BD6C *Lagenorhynchus australis*; BD6G *Lagenorhynchus obliquidens*; CC6A *Lobodon carcinophaga (Lobodon carcinophagus)*; CC10A *Mirounga angustirostris*; CA6A *Otaria flavescens*; CA8A *Phocarctos hookeri*; BD19A *Tursiops catalania (Tursiops aduncus)*; CA9A *Zalophus californianus*; BC9A *Ziphius cavirostris*. (Other All-cuts scientific names map 1:1 to the common-name codes above, e.g. AC1E *Balaenoptera musculus*, AB1A *Eschrichtius robustus*, BG2A *Inia geoffrensis*, BF2A *Phocoena phocoena*, BF4A *Phocoenoides dalli*, BF6A *Neophocaena phocaenoides*, DB1B *Trichechus manatus*, CD1A *Enhydra lutris*, CC12V *Phoca vitulina*, CC12H *Pusa hispida*, CC12F *Histriophoca fasciata*, CC12L *Phoca largha*, CC3A *Halichoerus grypus*, CC1A *Cystophora cristata*, CA3B *Eumetopias jubatus*, CA1F *Arctocephalus forsteri*, CA1P *Arctocephalus philippii*, BD1A *Cephalorhynchus commersonii*, BD1C *Cephalorhynchus heavisidii*, BD3A *Delphinus capensis (Delphinus bairdii)*, BD6H *Lagenorhynchus obscurus*, BD12A *Sotalia borneensis*, BD12B *Sotalia fluviatilis*.) Code scheme: A = mysticetes, B = odontocetes, C = pinnipeds/otter, D = sirenians.

### DCLDE 2027 killer-whale labels (from the Sci Data paper)
ClassSpecies: `KW` (killer whale), `HW` (humpback), `AB` (abiotic), `UndBio` (undetermined biological). Ecotype: `SRKW`, `NRKW`, `TKW` (Bigg's/transient), `OKW` (offshore), `SAR` (Southern Alaska Resident).

### DCLDE 2018 high-frequency classes (verbatim)
*Mesoplodon europaeus* Gervais' beaked whale; *Ziphius cavirostris* Cuvier's beaked whale; *Mesoplodon bidens* Sowerby's beaked whale; *Lagenorhynchus acutus* Atlantic white-sided dolphin; *Grampus griseus* Risso's dolphin; *Globicephala macrorhynchus* short-finned pilot whale; *Stenella* sp.; Delphinid type A; Delphinid type B; Unidentified delphinid. Low-frequency: *Balaenoptera musculus* tonal calls; *Eubalaena glacialis* up-calls.

### Google multispecies-whale classes (research.google blog)
Humpback; killer whale (calls, echolocation, whistles); blue; fin; minke (boing); Bryde's (biotwang); North Atlantic right whale; North Pacific right whale (gunshot, upcall). 8 species / 12 classes.

### BEANS `watkins` (datasets.yml)
31 classes after dropping Weddell_Seal; names use underscores, e.g. `Bottlenose_Dolphin`, `Humpback_Whale`, `Killer_Whale`, `Walrus` (full list = the 32 Best-of species above, minus Weddell Seal).

## Notes / caveats
- Watkins Kaggle mirror: 404; Kaggle competition/model pages are client-rendered so file sizes/licenses on Kaggle are U (slugs are V via perch-hoplite source).
- DCLDE 2027 license conflict (bucket `CC-BY-4.0.txt` vs paper's CC BY-NC-ND 4.0) needs resolving with NCEI/authors before any commercial use.
- DCLDE 2022 SOEST site refused connections; DCLDE 2024 has no NCEI copy and needs the DRDC credentials from the report.
- Zenodo/Figshare full-text search APIs ranked off-topic records first; the Zenodo DOIs listed came from web search, not from API confirmation (except 15743034).
- Scratch files from the fetches are in `/tmp` (`watkins_index.html`, `wb_aa3a.html`, `wb_fullcuts.html`, `wb_about.html`, `zen.json`, `gbif.json`, `kg*.html`).
