2900xt/keiko-hackMIT/firmware/esp32-s3/sketch/hydro.cpp

//
// Samples the piezo follower on GPIO1 (ADC1_CH0) at a fixed rate from a
// high-priority FreeRTOS task paced by a hardware timer, and ships raw 12-bit
// ADC counts to the laptop in framed blocks over native USB CDC:
//
//   "KBLK" | seq | t0_us | dropped | n | n x int16 | crc16
//
//   seq      uint32  block counter
//   t0_us    uint32  esp_timer_get_time() at the first sample of the block
//   dropped  uint32  blocks overwritten because the sender could not keep up
//   n        uint16  samples in this block (BLOCK)
//   data     n x little-endian int16, raw ADC counts 0..4095
//   crc      uint16  CRC-16/CCITT-FALSE over everything before it
//
// Same shape as the UNO Q node's Bridge.notify("hydro/block", …), just on a
// wire with no message boundaries, hence the magic + CRC. USB CDC moves
// ~1 MB/s, so unlike the UNO Q's 115200-baud Bridge the sample rate is limited
// by the ADC conversion time (~25 us), not the link.
//
// Wi-Fi mode (no laptop): if sketch/wifi_config.h exists, the board joins that
// network and also sends each block as a ready-made KEIK datagram straight to
// the pipeline -- the packet python/main.py would otherwise build. The serial
// frames keep flowing whenever a host is attached, so both can be watched.

#include <Arduino.h>
#include <esp_timer.h>
#include <freertos/FreeRTOS.h>
#include <freertos/queue.h>
#include <freertos/semphr.h>
#include <freertos/task.h>

#if __has_include("wifi_config.h")
#include "wifi_config.h"                       // gitignored: copy wifi_config.h.example and fill it in
#include <WiFi.h>
#include <WiFiUdp.h>
#define KEIKO_WIFI 1
#else
#define KEIKO_WIFI 0
#endif

// ---- configuration ---------------------------------------------------------
static const uint32_t SAMPLE_PERIOD_US = 125;   // 8000 Hz. The 1 MHz timer makes this exact; the Python side still
                                                // measures the real rate from t0_us.
static const uint8_t  ADC_PIN          = 1;     // GPIO1 = ADC1_CH0. Stay on ADC1: ADC2 is unusable while Wi-Fi is on.
static const int      ADC_BITS         = 12;
static const size_t   BLOCK            = 256;   // samples per frame (512 bytes payload, ~31 frames/s at 8 kHz)
static const size_t   NBLOCKS          = 4;     // ring depth; sender may lag by NBLOCKS-1 blocks
static const BaseType_t SAMPLER_CORE   = 1;     // the app core (loop() runs there too; the sampler outranks it)

// ---- frame -----------------------------------------------------------------
struct __attribute__((packed)) FrameHeader {
  char     magic[4];
  uint32_t seq;
  uint32_t t0_us;
  uint32_t dropped;
  uint16_t n;
};

// KEIK datagram (see python/main.py PACKET FORMAT); built on the board in Wi-Fi mode
struct __attribute__((packed)) KeikHeader {
  char     magic[4];
  uint8_t  ver, node, fmt, bits;
  float    fs;
  uint32_t seq;
  uint64_t t_ns;
  uint16_t n;
};

static uint16_t crc16_ccitt(uint16_t crc, const uint8_t* p, size_t len) {
  while (len--) {
    crc ^= (uint16_t)(*p++) << 8;
    for (int i = 0; i < 8; i++) crc = (crc & 0x8000) ? (crc << 1) ^ 0x1021 : crc << 1;
  }
  return crc;
}

// ---- sampler <-> sender plumbing ------------------------------------------
static int16_t  ring[NBLOCKS][BLOCK];
static uint32_t ring_t0_us[NBLOCKS];
static uint32_t dropped_blocks = 0;

static QueueHandle_t     ready_q;     // depth NBLOCKS-1 keeps the block being filled private
static SemaphoreHandle_t tick_sem;    // binary: late ticks coalesce instead of piling up
static hw_timer_t*       tick_timer;

static void IRAM_ATTR on_tick() {
  BaseType_t woken = pdFALSE;
  xSemaphoreGiveFromISR(tick_sem, &woken);
  if (woken) portYIELD_FROM_ISR();
}

static void sampler(void*) {
  uint8_t b = 0;
  size_t  i = 0;
  ring_t0_us[b] = (uint32_t)esp_timer_get_time();
  for (;;) {
    xSemaphoreTake(tick_sem, portMAX_DELAY);
    int raw = analogRead(ADC_PIN);
    if (raw < 0) raw = 1 << (ADC_BITS - 1);   // adc error -> mid-scale, keeps timing intact
    ring[b][i++] = (int16_t)raw;
    if (i == BLOCK) {
      i = 0;
      if (xQueueSend(ready_q, &b, 0) == pdTRUE) {
        b = (b + 1) % NBLOCKS;
      } else {
        dropped_blocks++;                     // sender is behind: reuse this block, keep sampling
      }
      ring_t0_us[b] = (uint32_t)esp_timer_get_time();
    }
  }
}

// ---- Wi-Fi -----------------------------------------------------------------
#if KEIKO_WIFI
static WiFiUDP udp;
static float   fs_measured = 0;               // from consecutive block timestamps, same estimator as main.py
static uint32_t last_t0_us = 0;
static bool     have_last  = false;

static void wifi_begin() {
  WiFi.mode(WIFI_STA);
  WiFi.setSleep(false);                       // modem sleep adds 100s of ms of jitter to UDP sends
  WiFi.begin(KEIKO_WIFI_SSID, KEIKO_WIFI_PSK);
  WiFi.setAutoReconnect(true);                // dropouts are the node's problem, not the pipeline's
}

static void send_keik(uint32_t seq, uint32_t t0_us, const uint8_t* data) {
  if (have_last && seq) {                     // measure fs across consecutive blocks (blocks are never reordered here)
    uint32_t dt = t0_us - last_t0_us;
    if (dt) {
      float fs = BLOCK * 1e6f / dt;
      fs_measured = fs_measured == 0 ? fs : 0.9f * fs_measured + 0.1f * fs;
    }
  }
  last_t0_us = t0_us; have_last = true;
  if (WiFi.status() != WL_CONNECTED) return;

  KeikHeader k = {{'K', 'E', 'I', 'K'}, 1, KEIKO_NODE_ID, 0, (uint8_t)ADC_BITS, fs_measured, seq,
                  (uint64_t)esp_timer_get_time() * 1000ULL, (uint16_t)BLOCK};
  udp.beginPacket(KEIKO_UDP_HOST, KEIKO_UDP_PORT);
  udp.write(reinterpret_cast<const uint8_t*>(&k), sizeof k);
  udp.write(data, BLOCK * sizeof(int16_t));
  udp.endPacket();
}
#endif

// ---- Arduino ---------------------------------------------------------------
void setup() {
  Serial.begin(921600);                       // baud is ignored on native USB CDC; matters only if Serial is a UART
  Serial.setTxTimeoutMs(50);                  // no host reading -> writes give up instead of stalling the sender
#if KEIKO_WIFI
  wifi_begin();
#endif
  analogReadResolution(ADC_BITS);
  analogSetPinAttenuation(ADC_PIN, ADC_11db); // 0..~3.1 V full scale; the follower idles at ~1.7 V
  analogRead(ADC_PIN);                        // first call does the channel setup; do it before the timer starts

  tick_sem = xSemaphoreCreateBinary();
  ready_q  = xQueueCreate(NBLOCKS - 1, sizeof(uint8_t));
  xTaskCreatePinnedToCore(sampler, "hydro_sampler", 4096, NULL, configMAX_PRIORITIES - 1, NULL, SAMPLER_CORE);

  tick_timer = timerBegin(1000000);           // 1 MHz -> alarm counts are microseconds
  timerAttachInterrupt(tick_timer, on_tick);
  timerAlarm(tick_timer, SAMPLE_PERIOD_US, true, 0);
}

void loop() {
  static uint32_t seq = 0;
  uint8_t b;
  xQueueReceive(ready_q, &b, portMAX_DELAY);  // blocks (not spins), so the sampler task gets the CPU

  FrameHeader h = {{'K', 'B', 'L', 'K'}, seq++, ring_t0_us[b], dropped_blocks, (uint16_t)BLOCK};
  const uint8_t* data = reinterpret_cast<const uint8_t*>(ring[b]);
  uint16_t crc = crc16_ccitt(0xFFFF, reinterpret_cast<const uint8_t*>(&h), sizeof h);
  crc = crc16_ccitt(crc, data, BLOCK * sizeof(int16_t));

#if KEIKO_WIFI
  send_keik(h.seq, h.t0_us, data);
  if (!Serial) return;                        // no host on USB: don't let a backpressured CDC write slow the Wi-Fi path
#endif
  Serial.write(reinterpret_cast<const uint8_t*>(&h), sizeof h);
  Serial.write(data, BLOCK * sizeof(int16_t));
  Serial.write(reinterpret_cast<const uint8_t*>(&crc), sizeof crc);
}
